cybrneon/head-md-future-of-drawing/process/2023-12-12/readme.md

# Progress of the day

## The Device
This is THE device. With speakers inside, and the micro-switch.
<br>
This is a view without the textile cover on the speaker body.

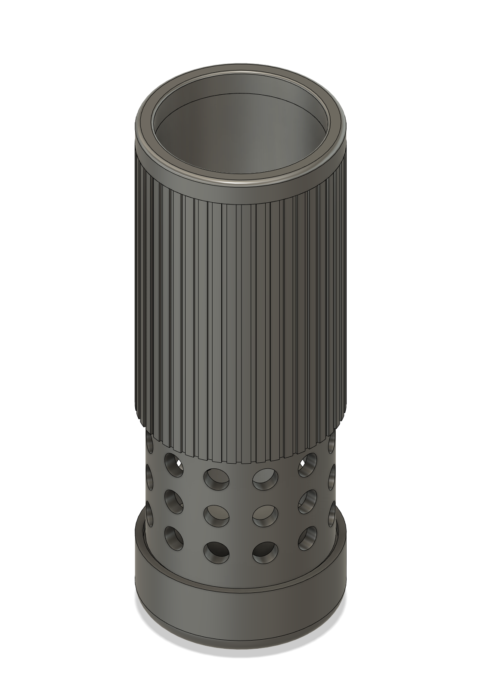
[picture p11: process/2023-12-12/screenshot_shape.png]


## The "Back Box" or "Black box"
This is the box where the RP4 is stored with all the cables, going to the device.

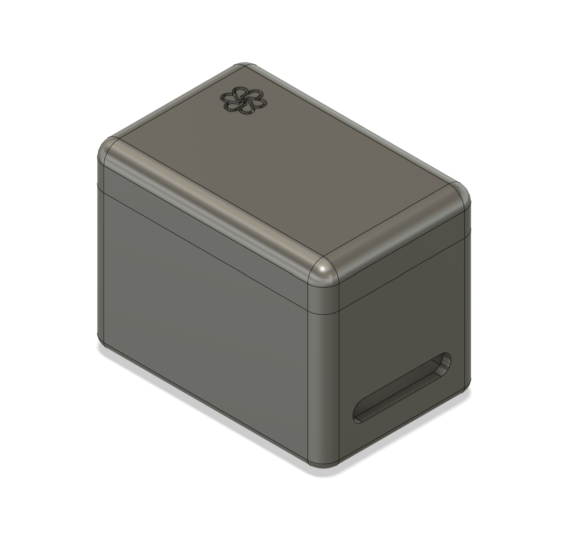
[picture p12: process/2023-12-12/screenshot_shape_blackbox.png]


## Ateliers
Sooooo, yesterday and today was the first day I put my feet in the Prototyping and Metal pool in my whole time at HEAD. So champagne 🍾🥂.
With Fred, I checked how I can make my shape and device come to reality. He told me I can do it with 3d printing. When I checked in the metal pool, Xavier told me that it wasn't possible to do there.

I also checked with the materials, and I think I'll need to find something suitable. For the "aluminium" part of my pen holder, I'll probably spray an aluminium color on it.

Here's a compilation of all the materials I saw there:

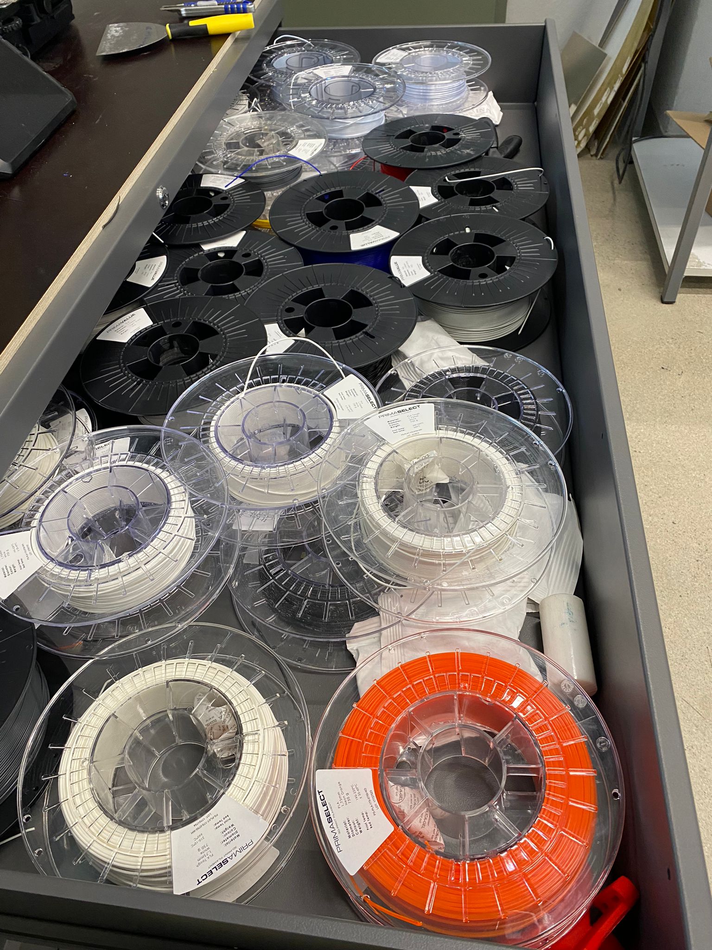
[picture p13: process/2023-12-12/WhatsApp Image 2023-12-12 at 14.30.54.jpeg]

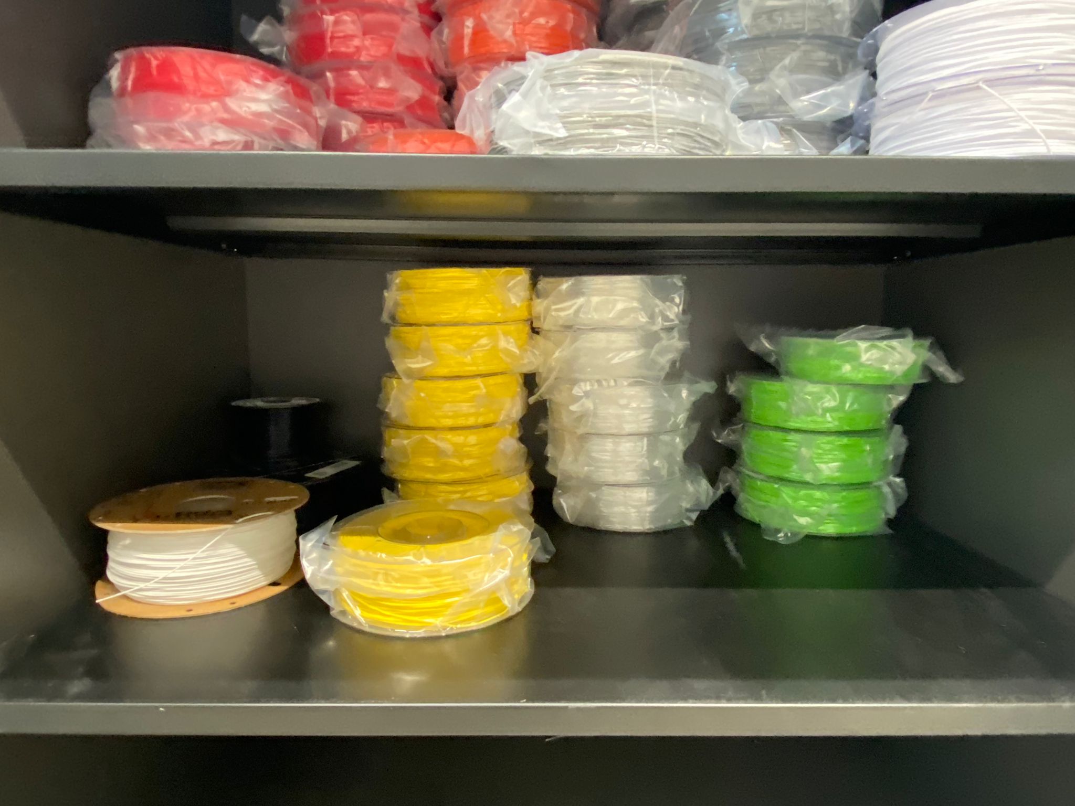
[picture p14: process/2023-12-12/WhatsApp Image 2023-12-12 at 14.30.55.jpeg]

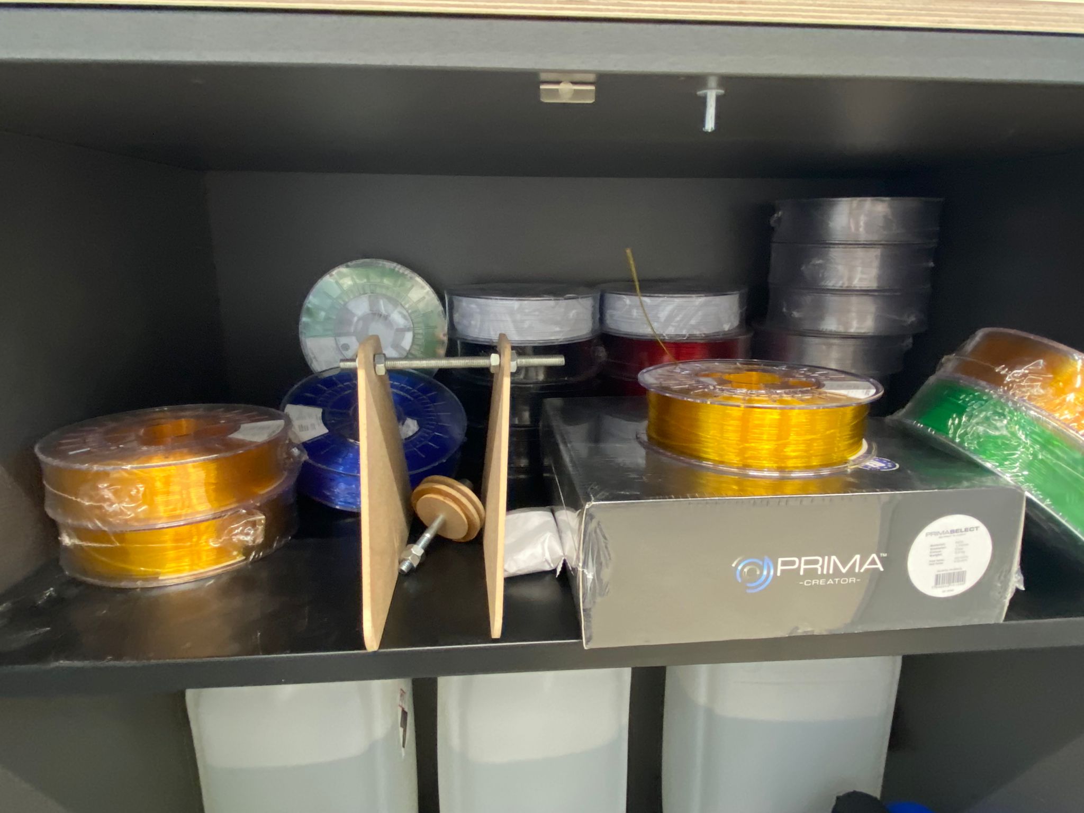
[picture p15: process/2023-12-12/WhatsApp Image 2023-12-12 at 14.30.55_1.jpeg]

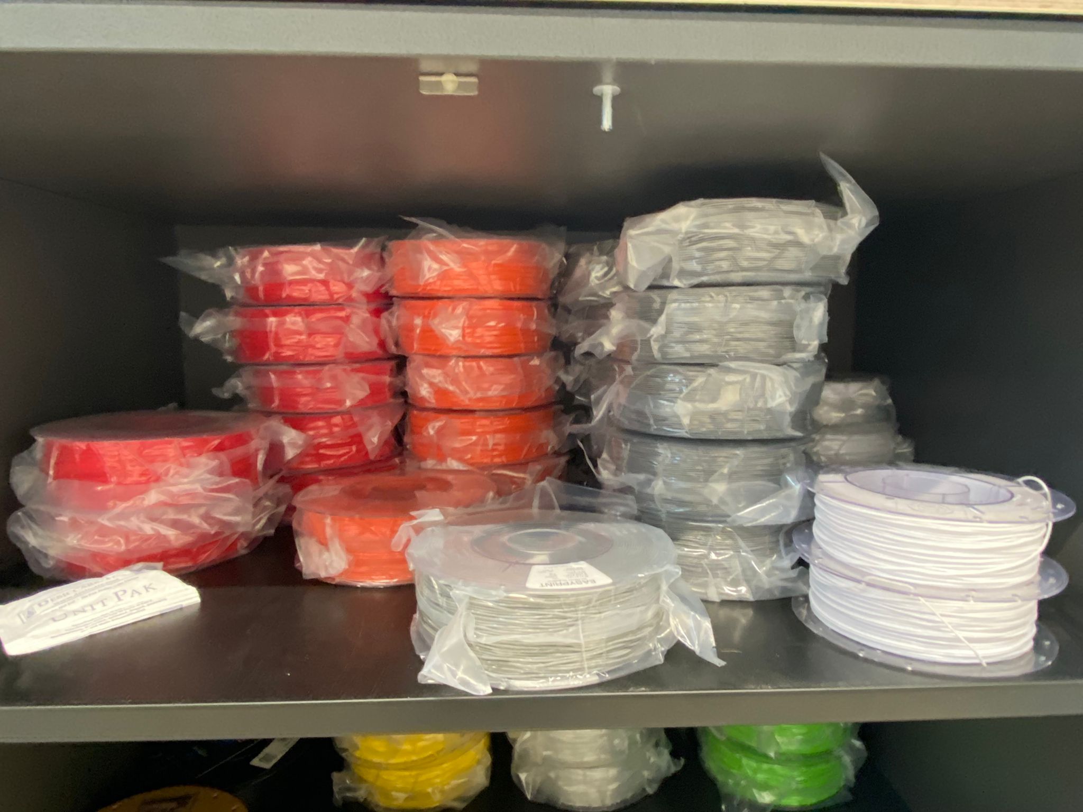
[picture p16: process/2023-12-12/WhatsApp Image 2023-12-12 at 14.30.56.jpeg]

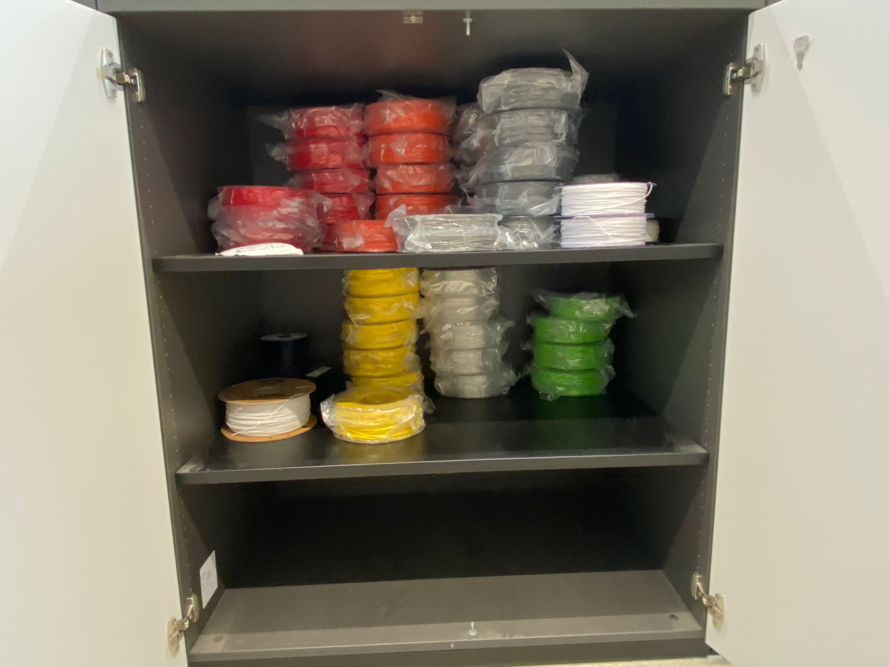
[picture p17: process/2023-12-12/WhatsApp Image 2023-12-12 at 14.30.56_1.jpeg]

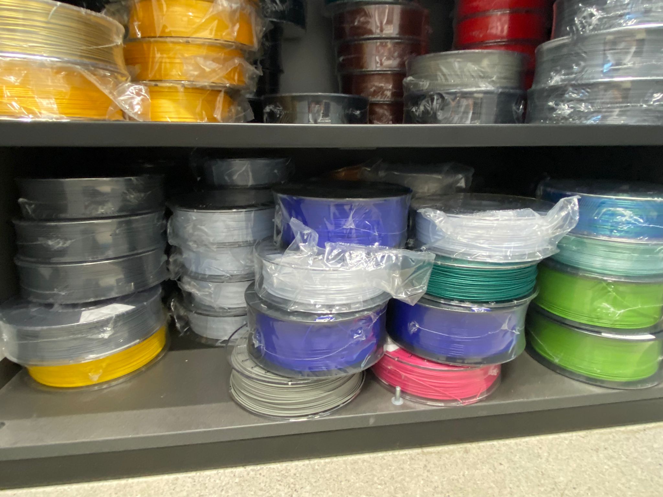
[picture p18: process/2023-12-12/WhatsApp Image 2023-12-12 at 14.30.57.jpeg]

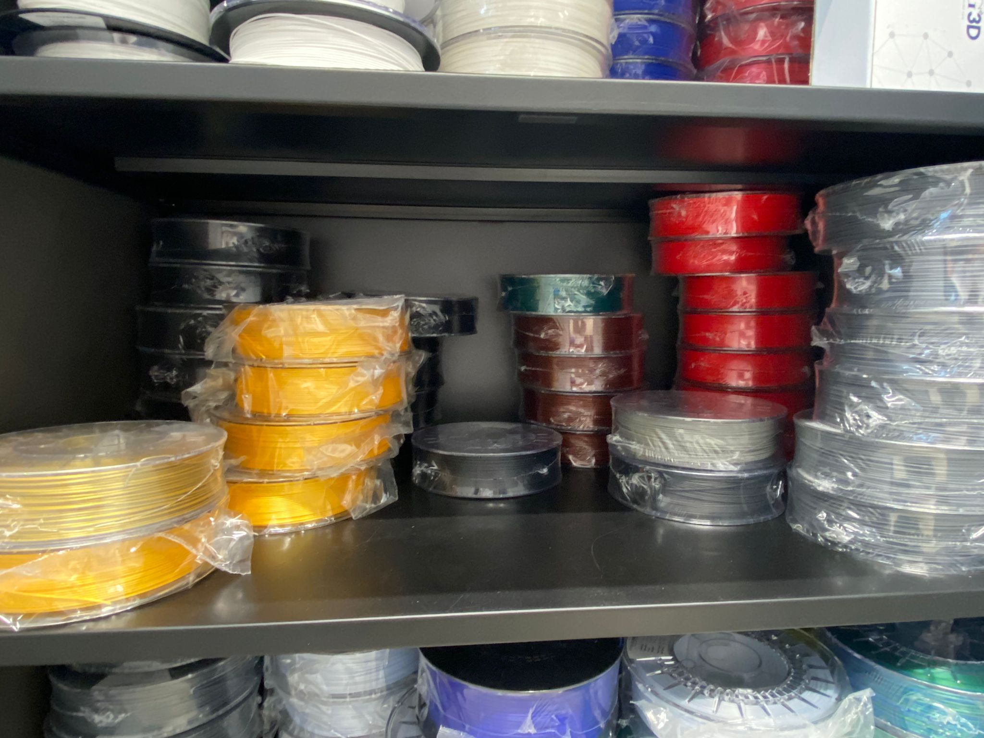
[picture p19: process/2023-12-12/WhatsApp Image 2023-12-12 at 14.30.57_1.jpeg]

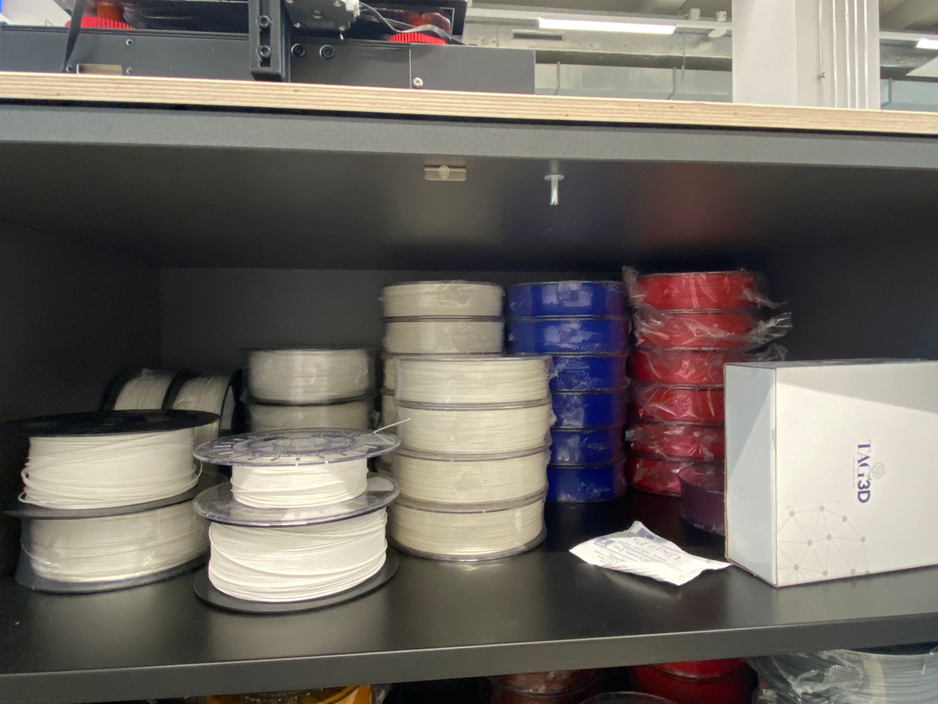
[picture p20: process/2023-12-12/WhatsApp Image 2023-12-12 at 14.30.58.jpeg]

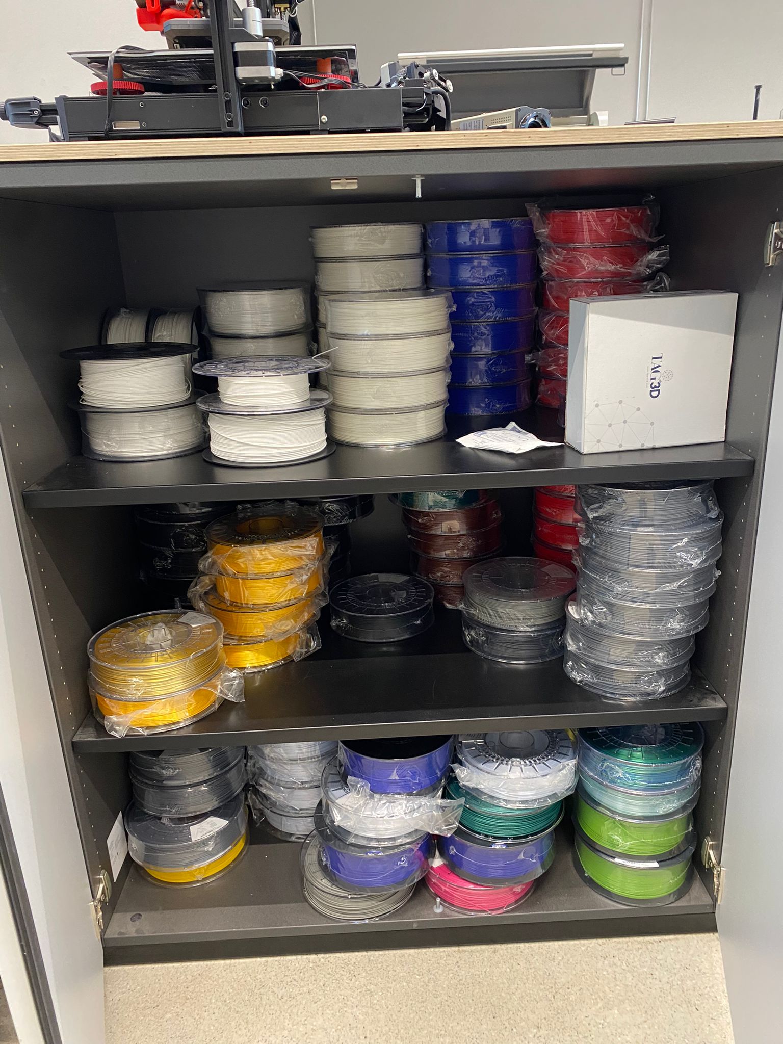
[picture p21: process/2023-12-12/WhatsApp Image 2023-12-12 at 14.30.58_1.jpeg]

<<<<<<< HEAD
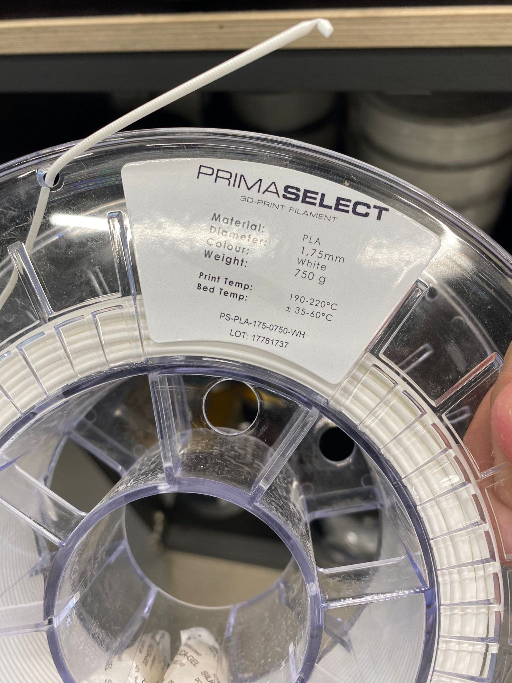
[picture p22: process/2023-12-12/WhatsApp Image 2023-12-12 at 14.30.59.jpeg]

=======


## Preparing for Test Day (D-2)

For the test day, I'm thinking of testing two stories and see what people like more, how they react to them, how inspired they are, etc.

Now I'm asking myself, what can I test on people who never seen or heard of the project?
<br>
-Stories.
<br>
What stories?
<br>
I can probably test the speed of the narration? like if there are blanks in between and if there are not?
<br>
I can also test with a voice synthesis and a recorded one?

### Story 1
Once upon a time, a river.
<br>
Rolling down the Akira Mountains, north of Selestia.
<br>
At the end of the river, a small village, built by a couple after they encountered diamonds in the river.
<br>
And this is why the river is called the Diamond River.
<br>
The couple, named Gigi governed the small village for a few years now, they have their own palace.
<br>
North of the village, a cook and shopkeeper, always ready to delight and make everyday special for the inhabitants of the village, by cooking a delicious stew for instance!
<br>
>>>>>>> parent of 233010a (wednesday morning work)
