cybrneon/head-md-future-of-drawing/process/2023-11-30/readme.md

# It's been a while since the last commit...

We had fun with Arduino, and discovered a lot. It's still a bit too technical, but I hope it will be okay.

## Pictures
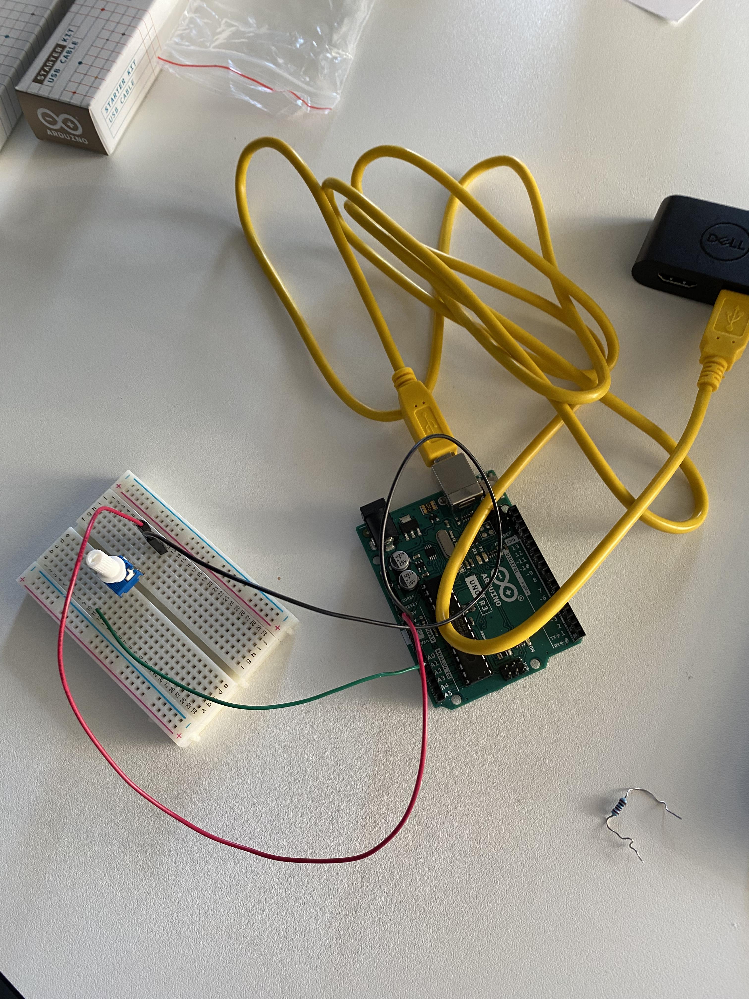
[picture p27: process/2023-11-30/IMG_6413.jpeg]

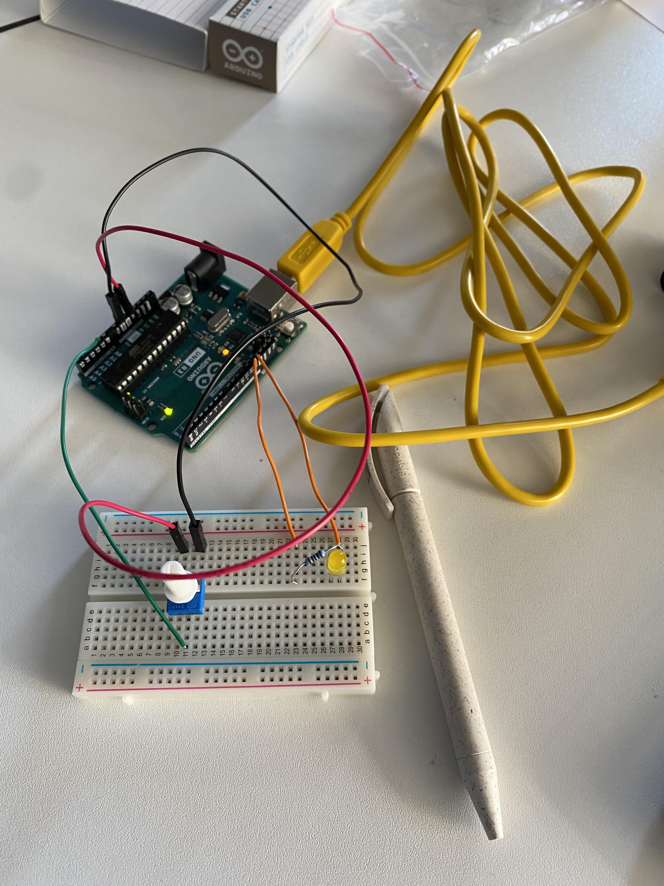
[picture p28: process/2023-11-30/IMG_6414.jpeg]

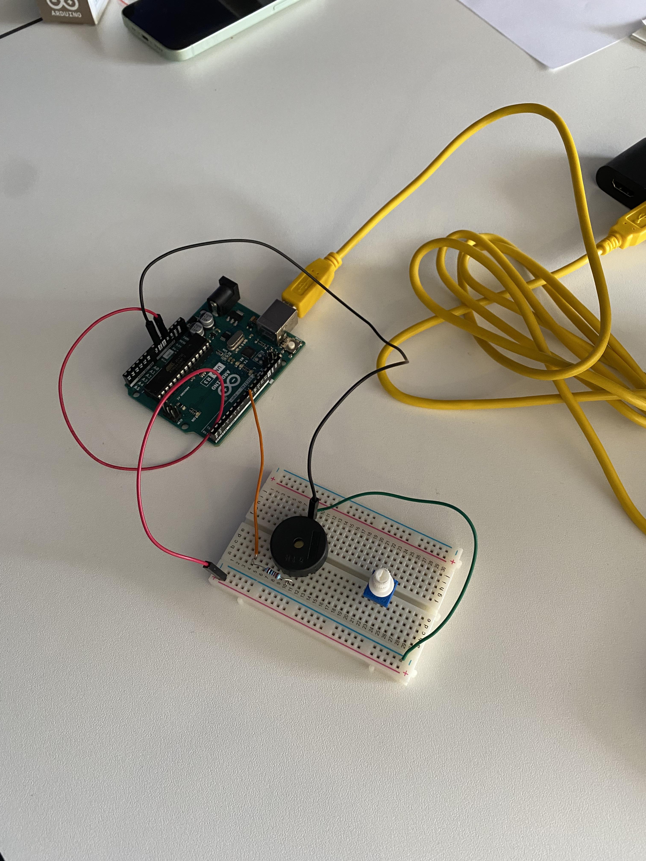
[picture p29: process/2023-11-30/IMG_6421.jpeg]


## Videos
Videos are available on the repo
