cybrneon/head-md-future-of-drawing/process/2023-10-26/readme.md

# Experimentation
We then started to imagine interactions and paper experiments with our subjects. I didn't know how or where to start, so I came back to the cards and drew ones that I then executed into paper prototypes.

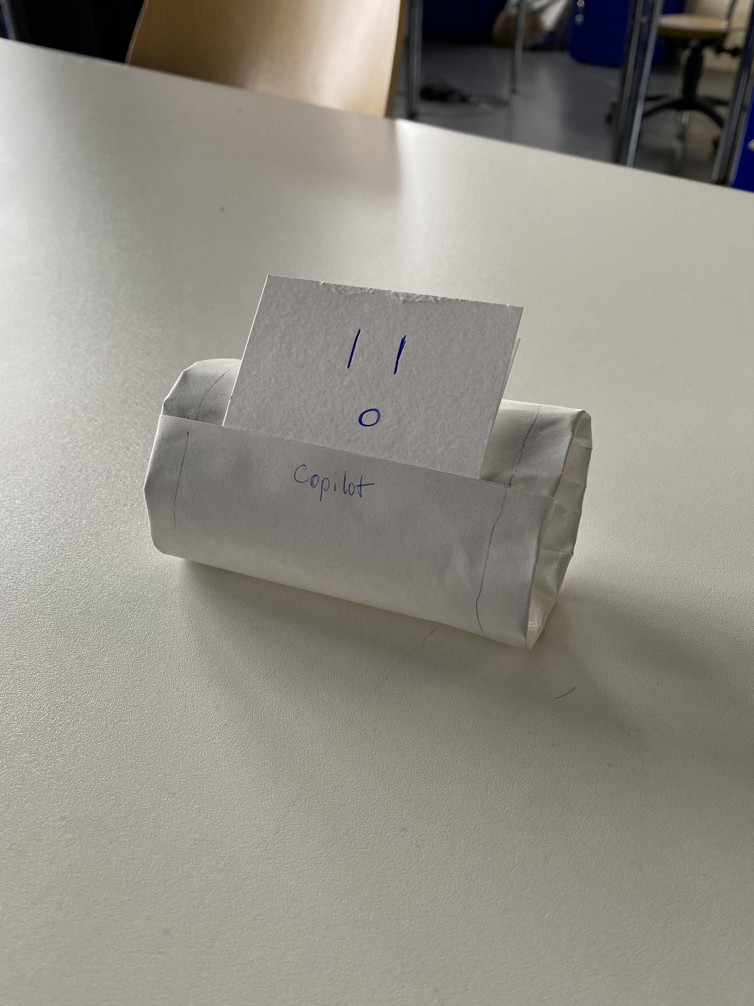
[picture p42: process/2023-10-26/20231026_115851675_iOS.jpeg]
Little Cute Copilot

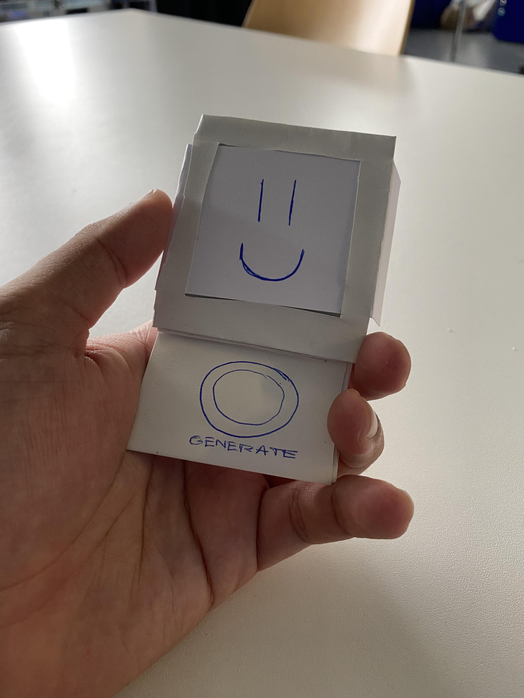
[picture p43: process/2023-10-26/20231026_115932319_iOS.jpeg]
Tamagotchi-like Drawing Experience Generator

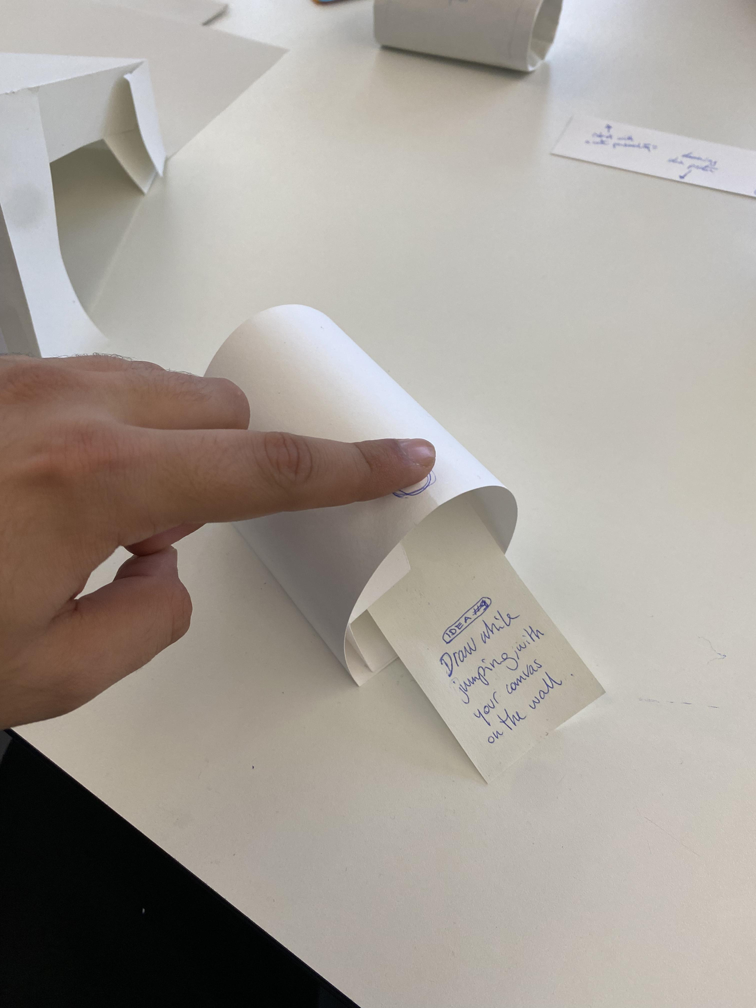
[picture p44: process/2023-10-26/20231030_092805427_iOS.jpeg]
Drawing Experience Generator Printer
