cybrneon/head-md-future-of-drawing/process/2023-12-13/readme.md

# Test Day Prep

## Call with Douglas
We need to have goals. I need to ask questions for me.
> I'm thinking probably testing one story reading it with pauses and seeing how people react and absorb the information to end up drawing. And the same story where I read it in a go without pauses?

This is too subtle!
<br>
I need to see the nature of the story
How much information I give to the user, How much I give to the person that's going to draw.

## Story 1 - original
Once upon a time, a river.
<br>
<br>
Rolling down the Akira Mountains, north of the coutry of Selestia.
<br>
<br>
At the end of the river, a small village, built by a couple after they encountered diamonds in the river.
<br>
<br>
And this is why the river is called the Marvelous Diamond River.
<br>
<br>
The couple, named Gigi governed the small village for a few years now, they even have their own palace.
<br>
<br>
Each year, the tradition states that every first of the month at 3PM, people run from the north to the south of the village, following the river, and dive into the Clear Blue Diamond Lake for a chance to find diamonds.
<br>
<br>
The lakeside is full of people coming from a number of different countries, here to witness the miracle, and why not be part of it.
<br>
<br>
That day in the crowd, a person by the name of Ash just finished their run and dive, was standing next to the lake thinking of what she'll be eating this evening.
<br>
<br>
Ash came to the lakeside with their dog, Ruffus.

## Story 1 - variation 1 (detailed with Bard)

In the heart of the majestic Akira Mountains, nestled amidst the snow-capped peaks and verdant valleys, flowed a magnificent river, its waters shimmering like a cascade of diamonds. This was the marvelous Diamond River, a source of wonder and fascination for the people of Selestia, the land that lay north of its meandering course.
<br>
<br>
Legends whispered of its magical origins, tales of a couple who stumbled upon its crystal-clear depths, discovering amidst the swirling currents a treasure of untold value – diamonds, embedded within the riverbed like glittering stars. Enthralled by their discovery, the couple established a small village at the river's end, naming it Diamond Village in honor of its precious namesake.
<br>
<br>
Over the centuries, the village grew in prosperity, its inhabitants living in harmony with the river's bounty. The villagers, guided by the wisdom of their ancestors, established a tradition that echoed the river's magical essence. Every first of the month, at the precise hour of three in the afternoon, they would embark on a grand procession, traversing the length of the village, following the river's winding path.
<br>
<br>
Upon reaching the Clear Blue Diamond Lake, a mesmerizing body of water that mirrored the heavens, the villagers would plunge into its depths, their hearts filled with anticipation. The lake, as if responding to their collective desire, would reveal its hidden treasures, scattering diamonds across the surface like a shower of celestial sparks.
<br>
<br>
This extraordinary spectacle drew visitors from far and wide, each hoping to witness the magical transformation and perhaps claim a diamond of their own. From the bustling streets of distant cities to the tranquil shores of neighboring kingdoms, people journeyed to Diamond Village, their eyes sparkling with excitement and a touch of disbelief.
<br>
<br>
On this particular first of the month, a young woman named Ash joined the throng of eager participants. Ash, accompanied by her loyal canine companion, Ruffus, had traveled from a distant land, her heart filled with a mix of curiosity and determination. She had heard tales of the Marvelous Diamond River and the village that lay at its end, tales of wonder and enchantment that had captured her imagination.
<br>
<br>
As the procession reached the Clear Blue Diamond Lake, Ash and Ruffus joined the mass of divers, their bodies plunging into the cool, refreshing waters. Around them, the air was filled with a collective gasp as the surface of the lake ignited with a dazzling display of diamonds, their brilliance reflecting the sun's radiant rays.
<br>
<br>
With hearts pounding and eyes wide with excitement, Ash and Ruffus emerged from the lake, their hands clutching their newfound treasures. Ash's heart swelled with joy as she held the sparkling diamond, its facets twinkling like a constellation of stars. She had not only witnessed the magic of the Marvelous Diamond River but had also become part of its enduring legend.
<br>
<br>
As the villagers celebrated their victory, Ash and Ruffus sat by the lakeside, savoring their newfound wealth and the memories of their extraordinary adventure. The sun began to set, casting a warm glow over the village and the majestic Akira Mountains, a perfect ending to a day filled with wonder and enchantment.

### -> Asking Bard to keep going with this story beggining
Ash and Ruffus were walking along the river bank, enjoying the cool breeze and the beautiful scenery of the Akira Mountains. The water in the river was crystal clear and sparkled in the sunlight, reflecting the lush green trees that lined the banks. Ash was lost in thought, thinking about the upcoming diamond dive. She had heard stories about people finding huge diamonds in the Clear Blue Diamond Lake, and she couldn't help but feel a little excited about the possibility of being one of them.
<br>
<br>
As they approached the lake, Ash could see the crowds of people already gathered on the shore. Everyone was eager to get into the water and start searching for diamonds. Ash and Ruffus joined the line and waited their turn.
<br>
<br>
Finally, it was Ash's turn to dive into the lake. She took a deep breath and plunged into the water. The water was cold and refreshing, and she could see the sunlight filtering down from the surface. She swam down to the bottom of the lake and started searching for diamonds.
<br>
<br>
After a few minutes, Ash spotted something shiny on the bottom of the lake. She swam over to it and picked it up. It was a small diamond, but it was still beautiful. Ash was thrilled! She swam back to the surface and showed the diamond to Ruffus, who wagged his tail excitedly.
<br>
<br>
Ash and Ruffus joined the other people who had found diamonds and celebrated their good fortune. They all agreed that it was a great day to be in Selestia.
<br>
<br>
Later that evening, Ash and Ruffus were enjoying a delicious dinner of grilled fish and vegetables. They were feeling very happy and content. Ash had had a wonderful day, and she was grateful for the opportunity to experience the miracle of the Marvelous Diamond River.

### -> Asking ChatGPT to keep going with this story beggining
As Ash caught her breath, she marveled at the sparkling water of the Clear Blue Diamond Lake. The sun dipped low on the horizon, casting a warm golden glow over the village and turning the water into a mesmerizing sea of reflections. Ruffus, her loyal dog, wagged his tail enthusiastically, seemingly as captivated by the spectacle as the humans around them.
<br>
<br>
The tradition of diving for diamonds had been a part of Ash's life for as long as she could remember. Her parents, avid treasure hunters, had regaled her with tales of their own diamond discoveries in the Marvelous Diamond River. Now, as an adult, Ash continued the family tradition, seeking not just wealth but also the thrill of the chase.
<br>
<br>
While many participants eagerly scanned the lake bed for the elusive gems, Ash's mind was preoccupied with a different kind of treasure – a cozy meal waiting for her at home. She had recently discovered a quaint little bakery in the village that boasted the most delectable pastries. As the sun dipped lower, Ash decided to wrap up her diamond quest and head to the bakery before it closed.
<br>
<br>
With Ruffus trotting faithfully by her side, Ash strolled through the lively village square. The air was filled with the sweet aroma of freshly baked goods, and the sound of laughter and chatter enveloped the surroundings. The villagers prepared for the evening festivities, which included a grand feast in celebration of the monthly ritual.
<br>
<br>
As Ash reached the bakery, she was greeted by the warm smile of the baker, an elderly woman named Elara, known for her culinary prowess. The tantalizing display of pastries and cakes beckoned Ash, and she couldn't resist ordering an assortment to enjoy later in the evening.
<br>
<br>
With a bag full of pastries in hand, Ash made her way back to the lakeside. The sun had dipped below the horizon, and the village was bathed in the soft glow of lanterns and the radiant moonlight. The excitement in the air was palpable as villagers prepared for the feast, sharing stories of their diamond dives and exchanging laughter.
<br>
<br>
Ash found a quiet spot by the lake, where the gentle lapping of the water provided a soothing backdrop. Ruffus settled down beside her, his eyes gleaming with contentment. As the villagers reveled in the festivities, Ash indulged in the delightful pastries, savoring each bite.
<br>
<br>
Little did she know that this seemingly ordinary evening held the promise of unexpected adventures and discoveries. The Marvelous Diamond River, with its mystical allure, was about to weave another chapter into the tapestry of Ash's life, one filled with intrigue and the magic of the Akira Mountains.

# Other Stuff
I've been thinking of a name for my project because I kept the project name "Morpheus Project". It's a project name, but I want a really cool name for my device and assistant. Why not keep Morpheus? or find another name?

I also tested 3d printing!
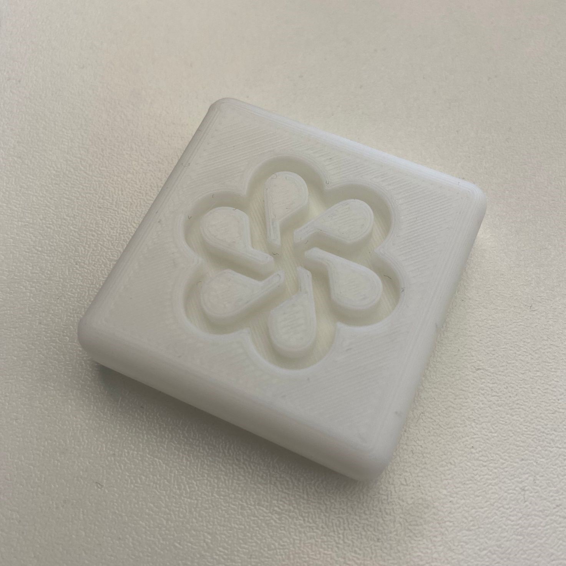
[picture p53: process/2023-12-13/3d_print_test.jpeg]
