cybrneon/head-md-future-of-drawing/process/2023-10-25/readme.md

# Prototyping? with Paper!
## First Try
At first, I drew the following cards:
- Inks
- Poker Face
- Figuration
- Peltier

I then made an interactive Captcha machine that asks you to draw something on it to confirm you're human, with a voice that asks you why you're drawing things the way you're drawing them and not giving any emotion.

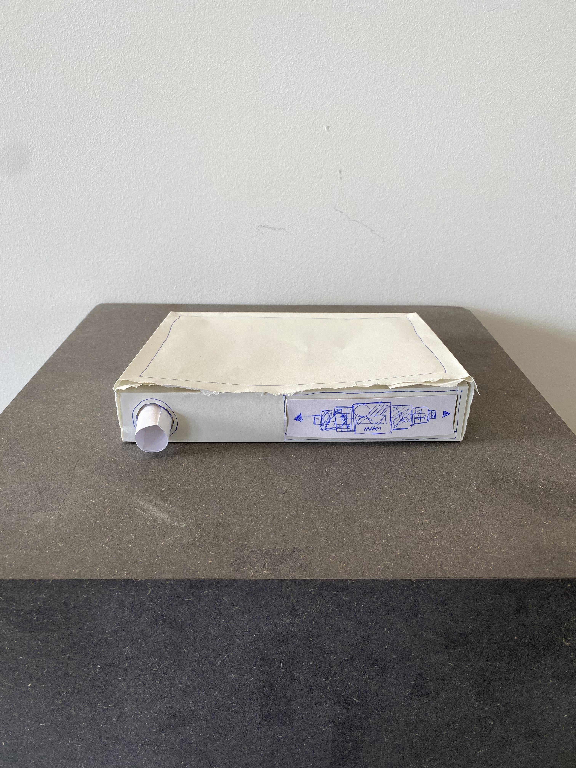
[picture p57: process/2023-10-25/20231025_130053381_iOS.jpeg]

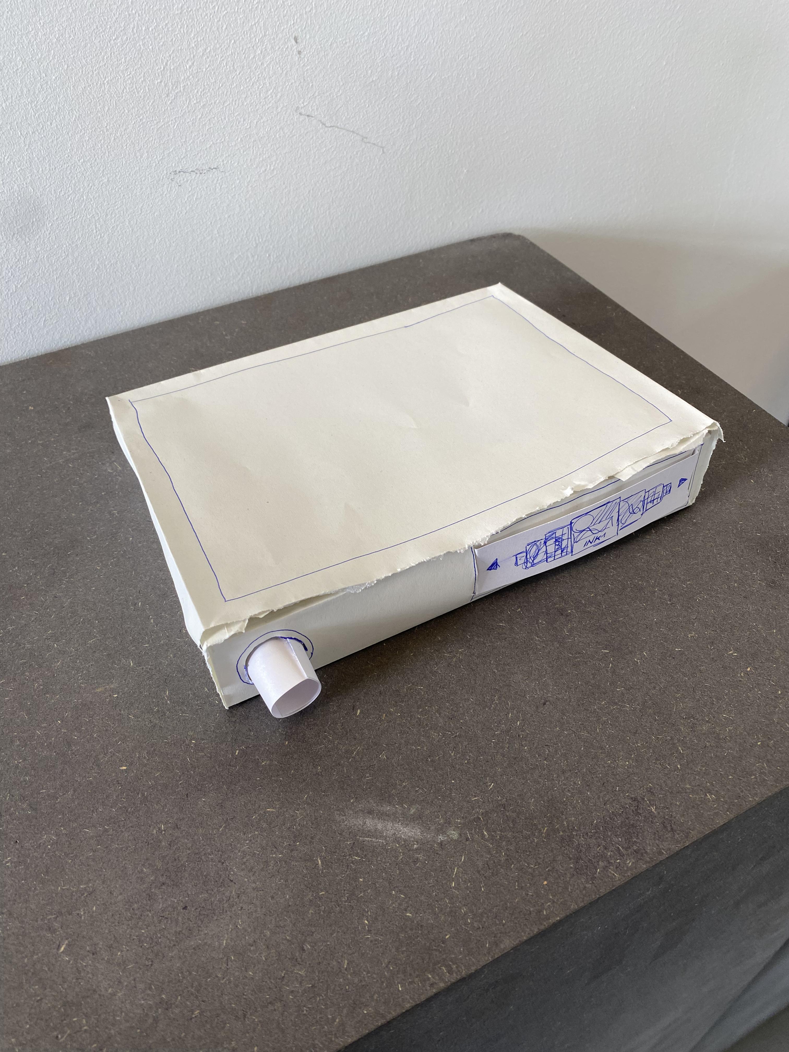
[picture p58: process/2023-10-25/20231025_130104790_iOS.jpeg]

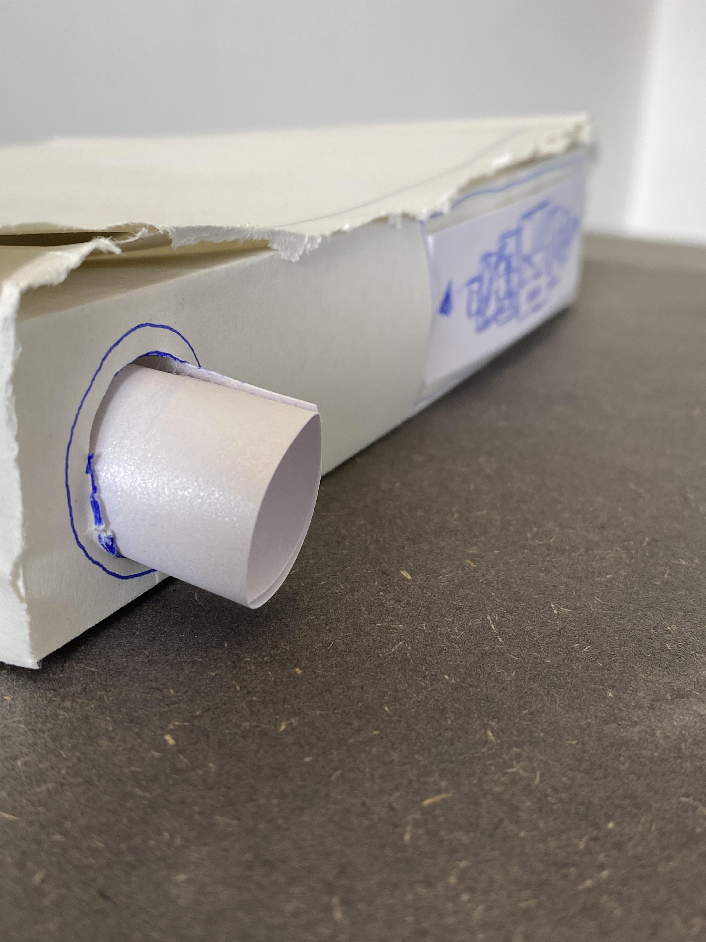
[picture p59: process/2023-10-25/20231025_130112993_iOS.jpeg]

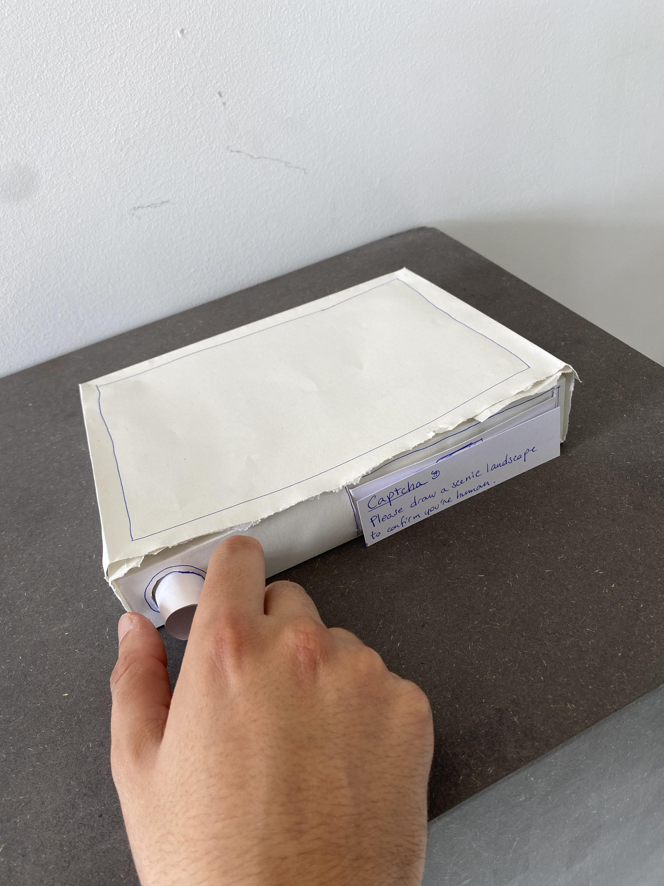
[picture p60: process/2023-10-25/20231025_130137430_iOS.jpeg]
