cybrneon/head-md-future-of-drawing/form/img/snapshot_shape2.png

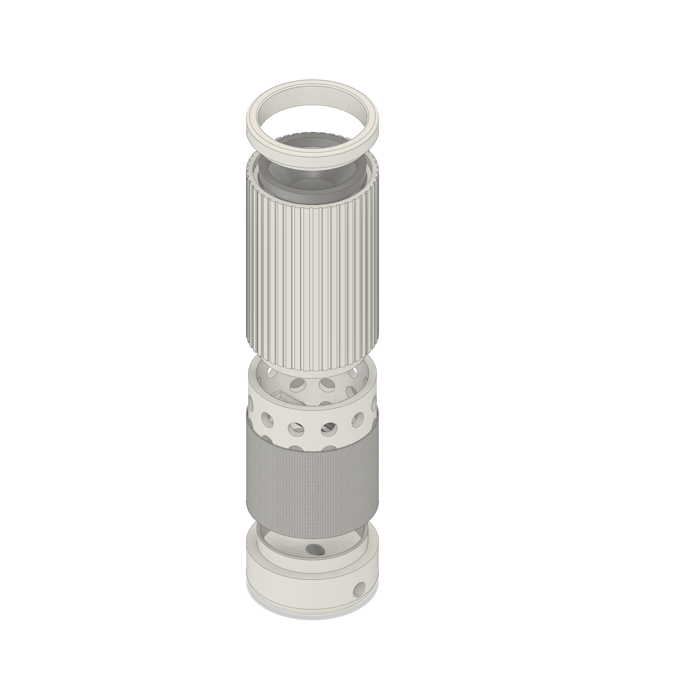
form/img/snapshot_shape2.png
