cybrneon/head-md-future-of-drawing/form/render/CdA_FinalSketch_render3.png

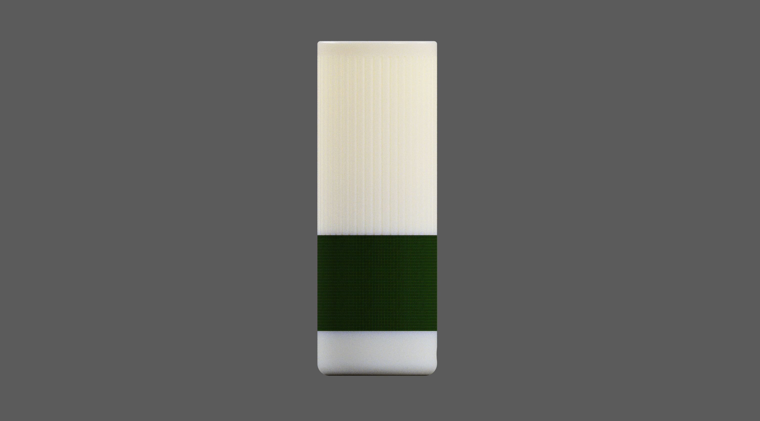
form/render/CdA_FinalSketch_render3.png
