cybrneon/head-md-future-of-drawing/presentations/branding/morpheus-beta-colorpalette.png

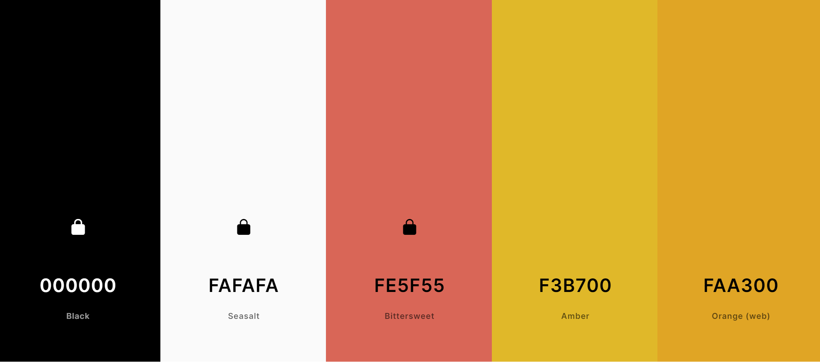
presentations/branding/morpheus-beta-colorpalette.png
