cybrneon/head-md-future-of-drawing/presentations/concept-presentation-2023-11-16/Dossier_CdA_Concept_InDesign/Links/IMG_6370.jpg

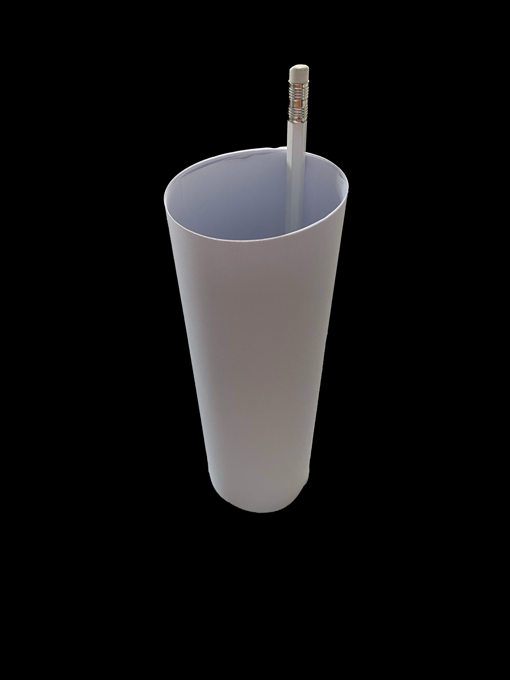
presentations/concept-presentation-2023-11-16/Dossier_CdA_Concept_InDesign/Links/IMG_6370.jpg
