cybrneon/head-md-future-of-drawing/presentations/concept-presentation-2023-11-16/Dossier_CdA_Concept_InDesign/Links/radio_1.jpg

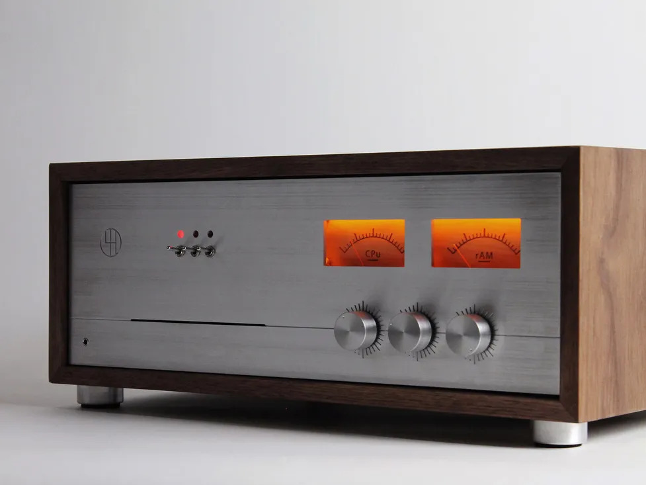
presentations/concept-presentation-2023-11-16/Dossier_CdA_Concept_InDesign/Links/radio_1.jpg
