cybrneon/head-md-future-of-drawing/presentations/final-presentation-folder-2024-01-17/Links/morpheus-userjourney.png

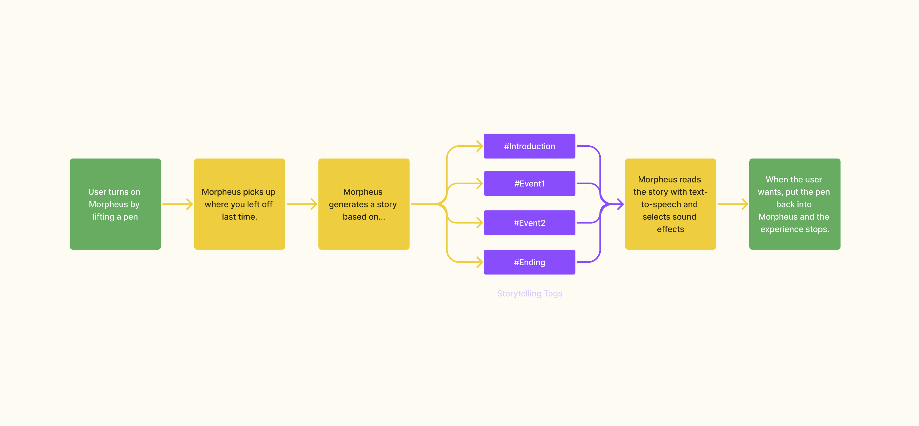
presentations/final-presentation-folder-2024-01-17/Links/morpheus-userjourney.png
