cybrneon/head-md-future-of-drawing/process/2023-10-19_20/20231019_132728396_iOS.jpeg

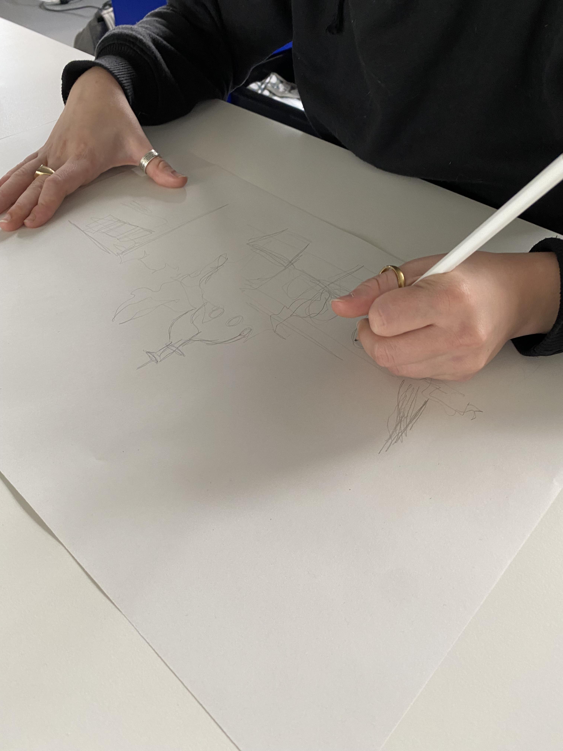
process/2023-10-19_20/20231019_132728396_iOS.jpeg
