cybrneon/head-md-future-of-drawing/process/2023-10-19_20/20231020_075834999_iOS.jpeg

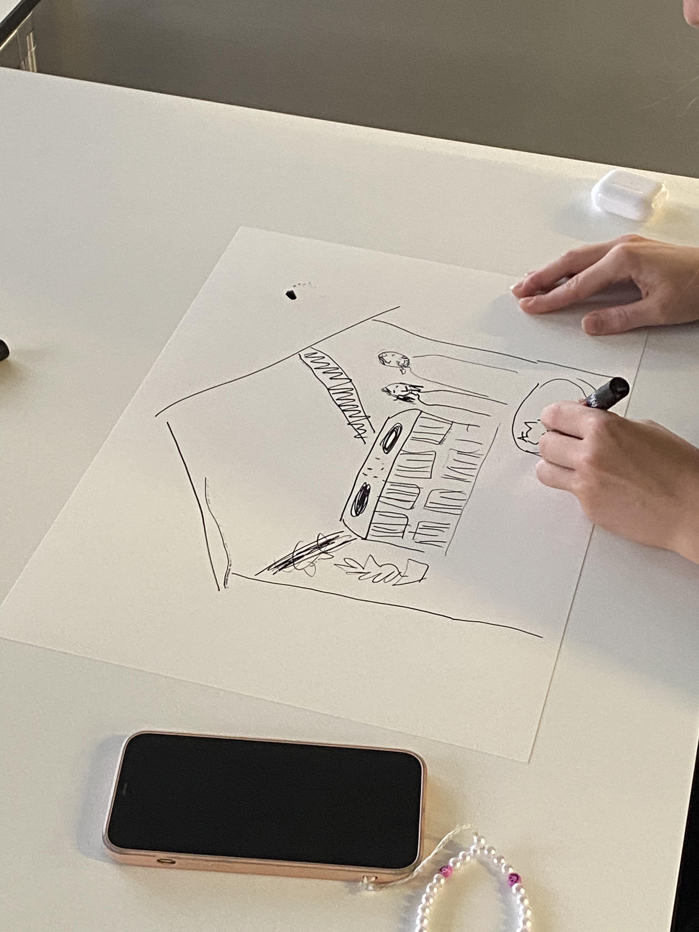
process/2023-10-19_20/20231020_075834999_iOS.jpeg
