cybrneon/head-md-future-of-drawing/process/2023-10-19_20/20231020_080150618_iOS.jpeg

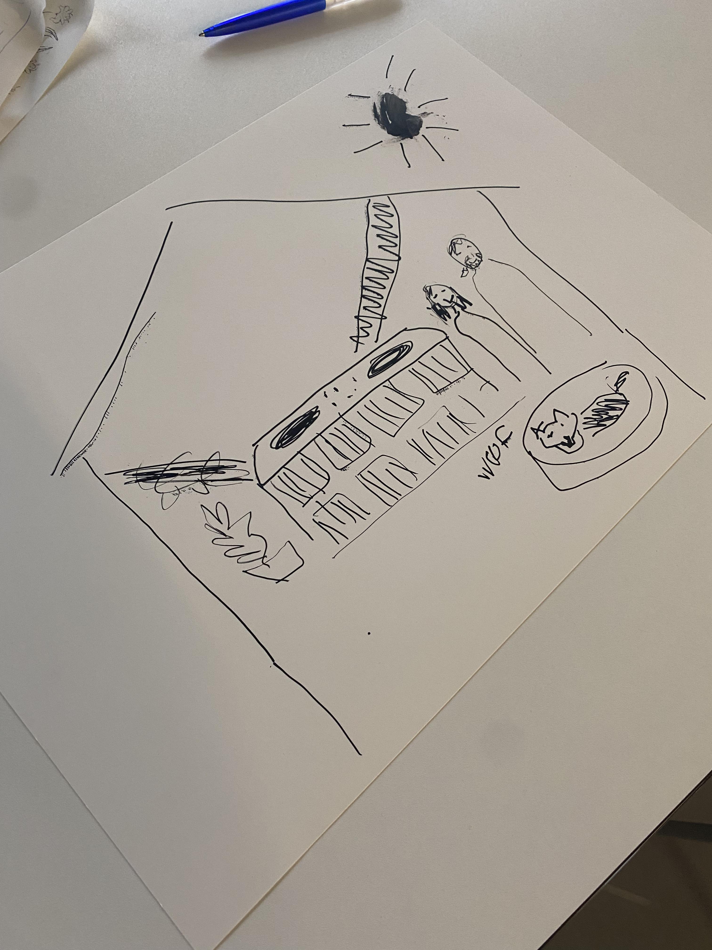
process/2023-10-19_20/20231020_080150618_iOS.jpeg
