cybrneon/head-md-future-of-drawing/process/2023-10-25/20231025_130244025_iOS.jpeg

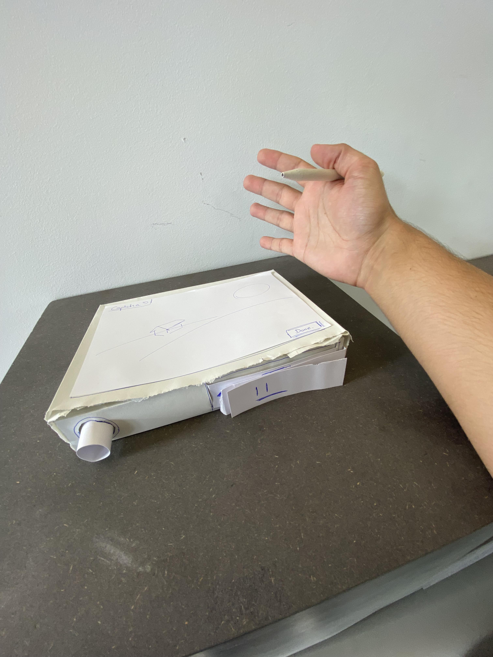
process/2023-10-25/20231025_130244025_iOS.jpeg
