cybrneon/head-md-future-of-drawing/process/2023-10-26/20231026_120012041_iOS.jpeg

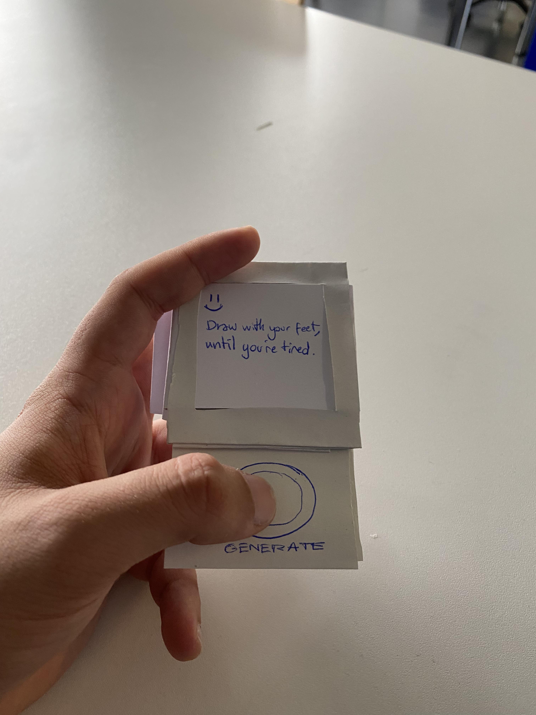
process/2023-10-26/20231026_120012041_iOS.jpeg
