cybrneon/head-md-future-of-drawing/process/2023-10-26/20231030_092759936_iOS.jpeg

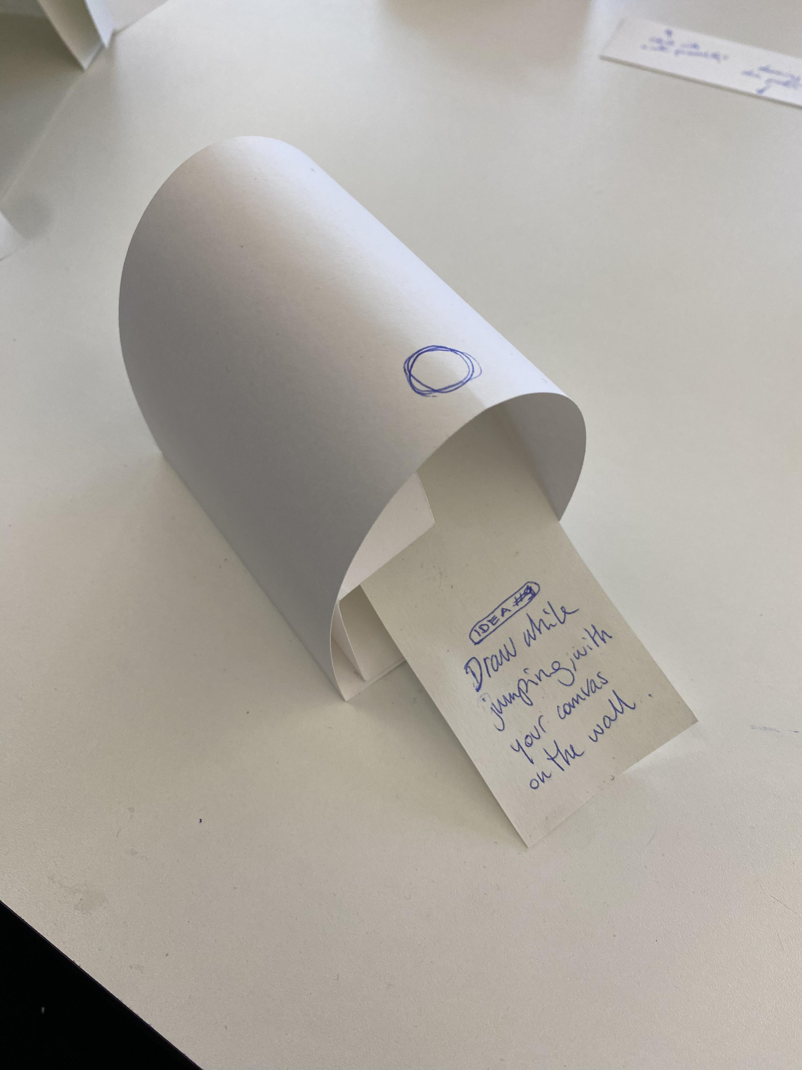
process/2023-10-26/20231030_092759936_iOS.jpeg
