cybrneon/head-md-future-of-drawing/process/2023-10-30/20231030_092852672_iOS.jpeg

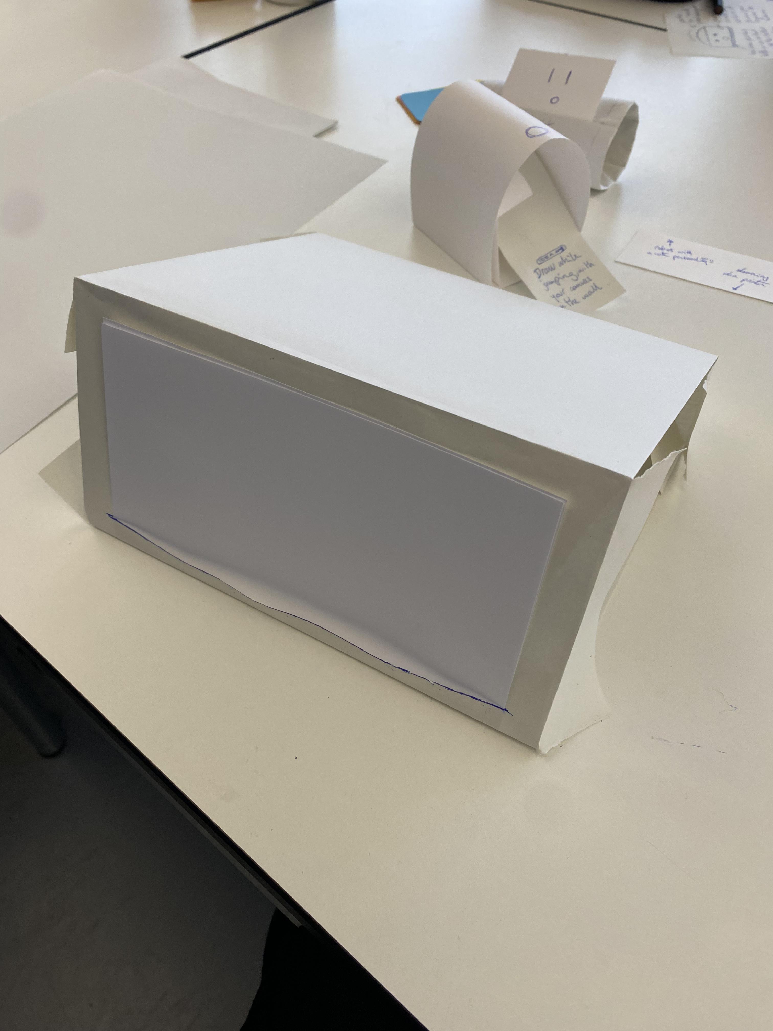
process/2023-10-30/20231030_092852672_iOS.jpeg
