cybrneon/head-md-future-of-drawing/process/2023-10-30/20231030_143424386_iOS.jpeg

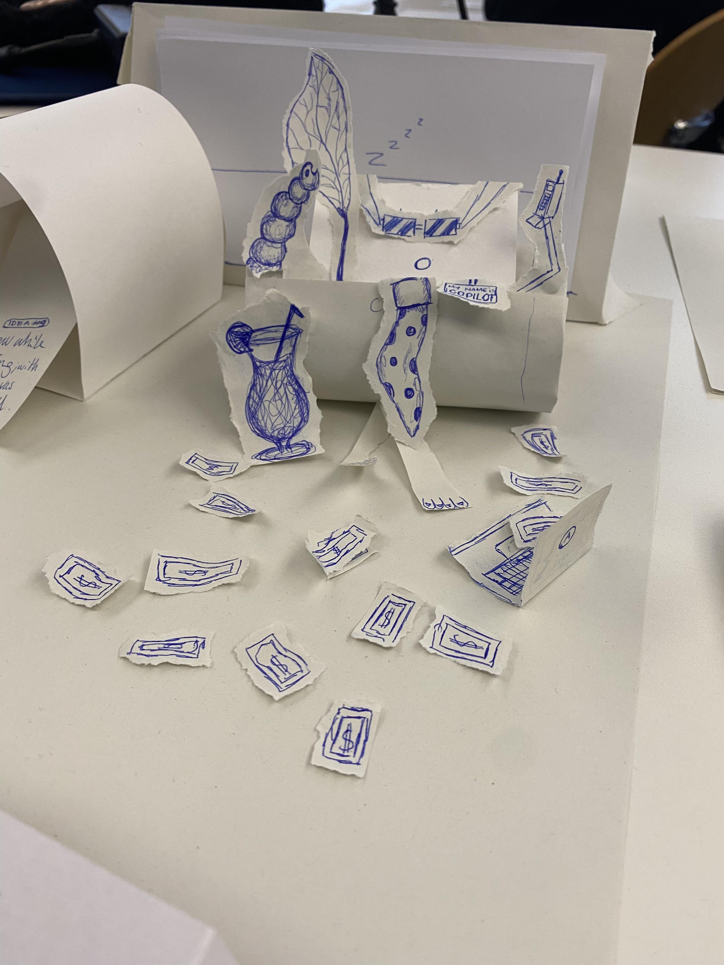
process/2023-10-30/20231030_143424386_iOS.jpeg
