cybrneon/head-md-future-of-drawing/process/2023-11-01/20231101_100316862_iOS.jpeg

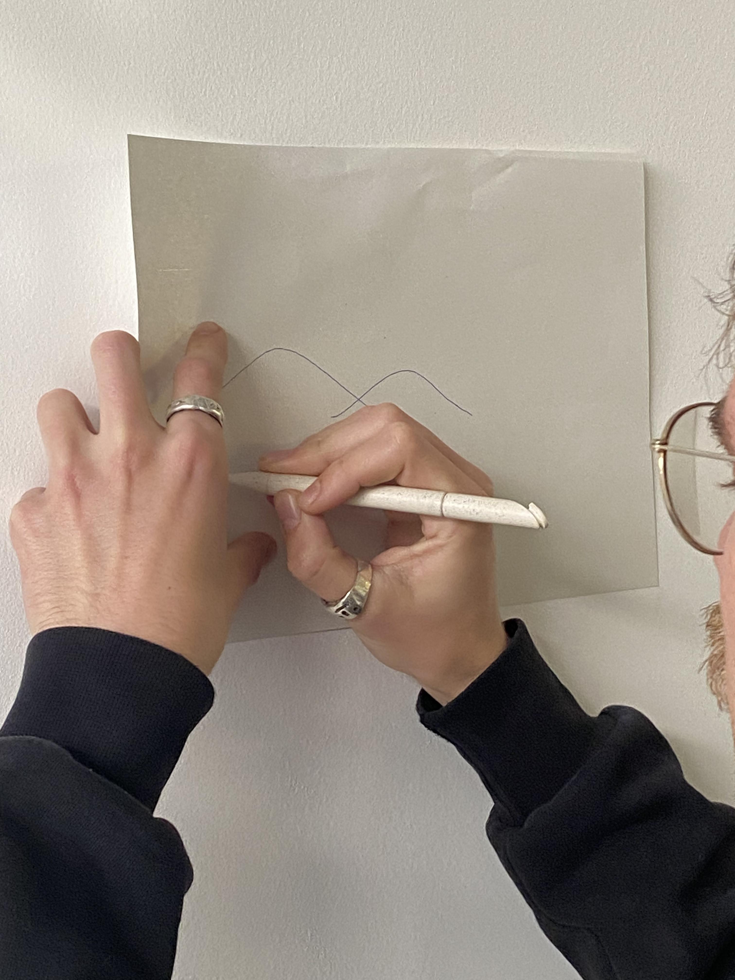
process/2023-11-01/20231101_100316862_iOS.jpeg
