cybrneon/head-md-future-of-drawing/process/2023-11-01/20231101_101724469_iOS.jpeg

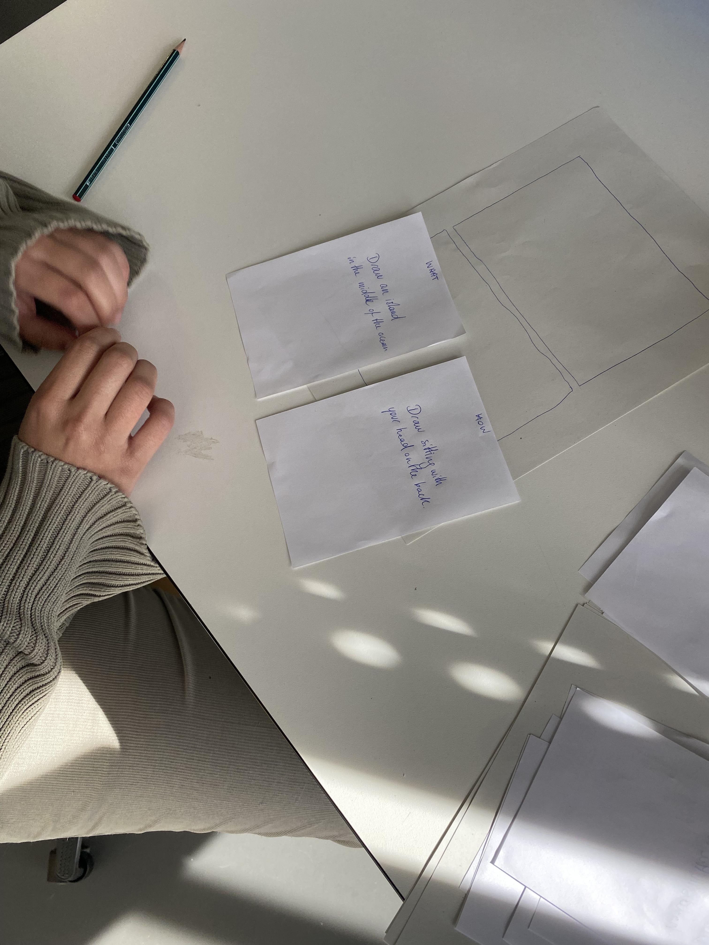
process/2023-11-01/20231101_101724469_iOS.jpeg
