cybrneon/head-md-future-of-drawing/process/2023-11-01/20231101_104921781_iOS.jpeg

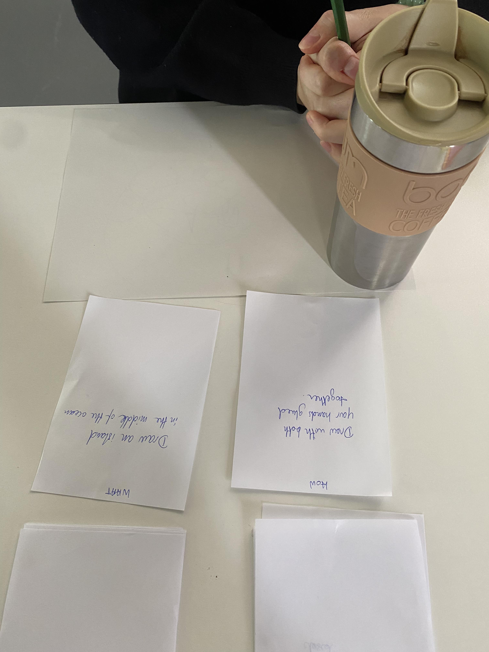
process/2023-11-01/20231101_104921781_iOS.jpeg
