cybrneon/head-md-future-of-drawing/process/2023-11-01/20231101_105053932_iOS.jpeg

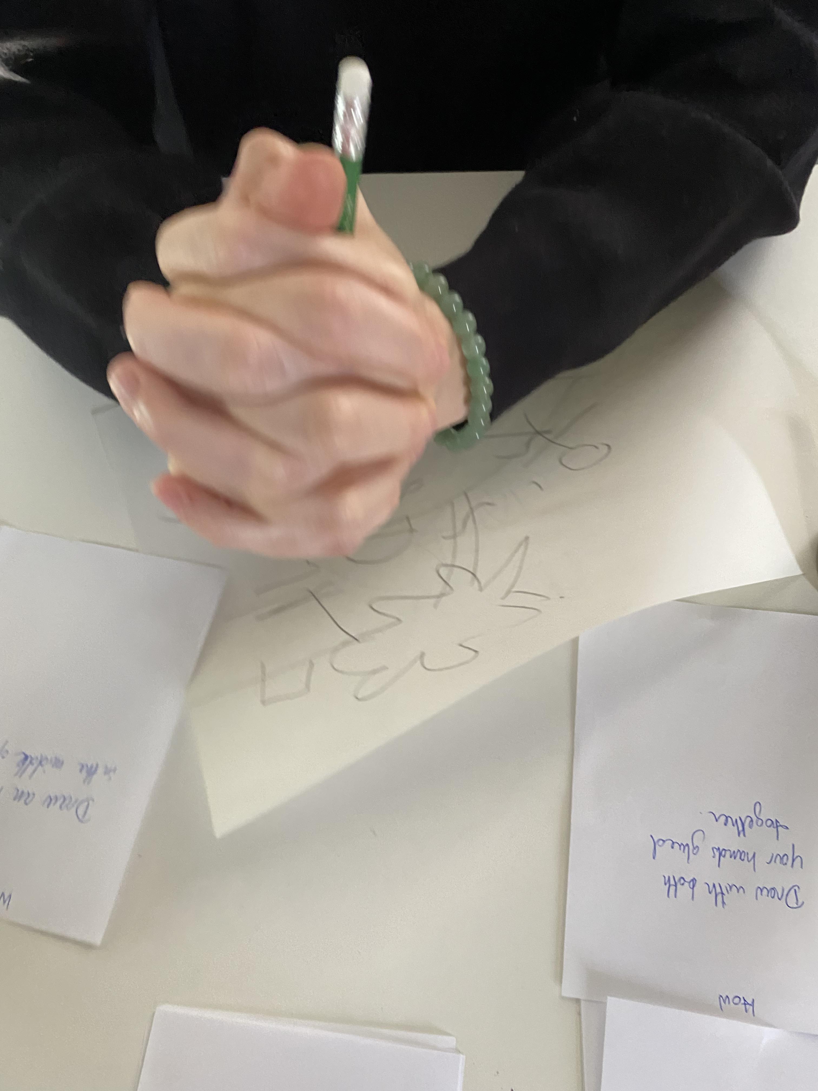
process/2023-11-01/20231101_105053932_iOS.jpeg
