cybrneon/head-md-future-of-drawing/process/2023-11-13/IMG_subject1_01.jpeg

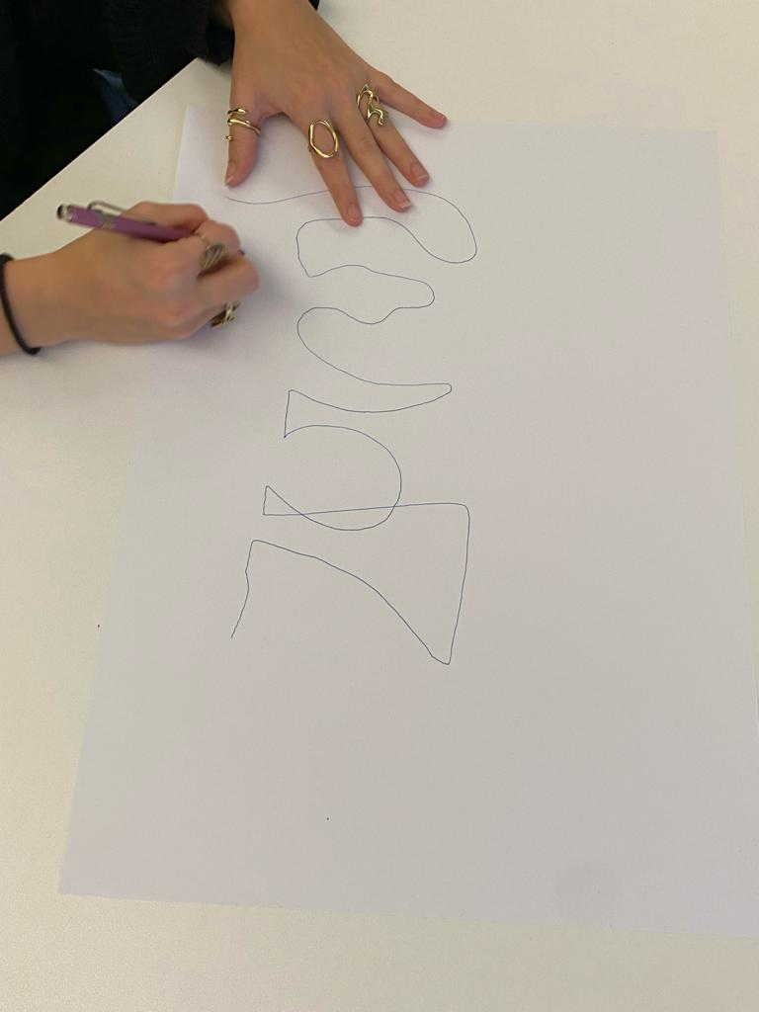
process/2023-11-13/IMG_subject1_01.jpeg
