cybrneon/head-md-future-of-drawing/process/2023-11-13/IMG_subject1_03.jpeg

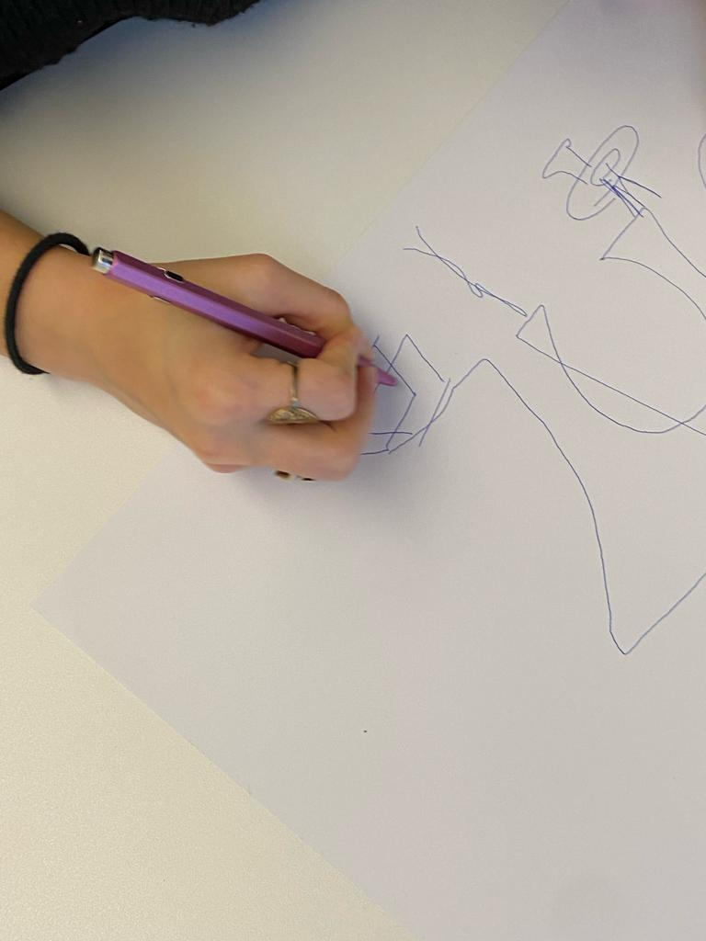
process/2023-11-13/IMG_subject1_03.jpeg
