cybrneon/head-md-future-of-drawing/process/2023-11-14/IMG_6363.jpeg

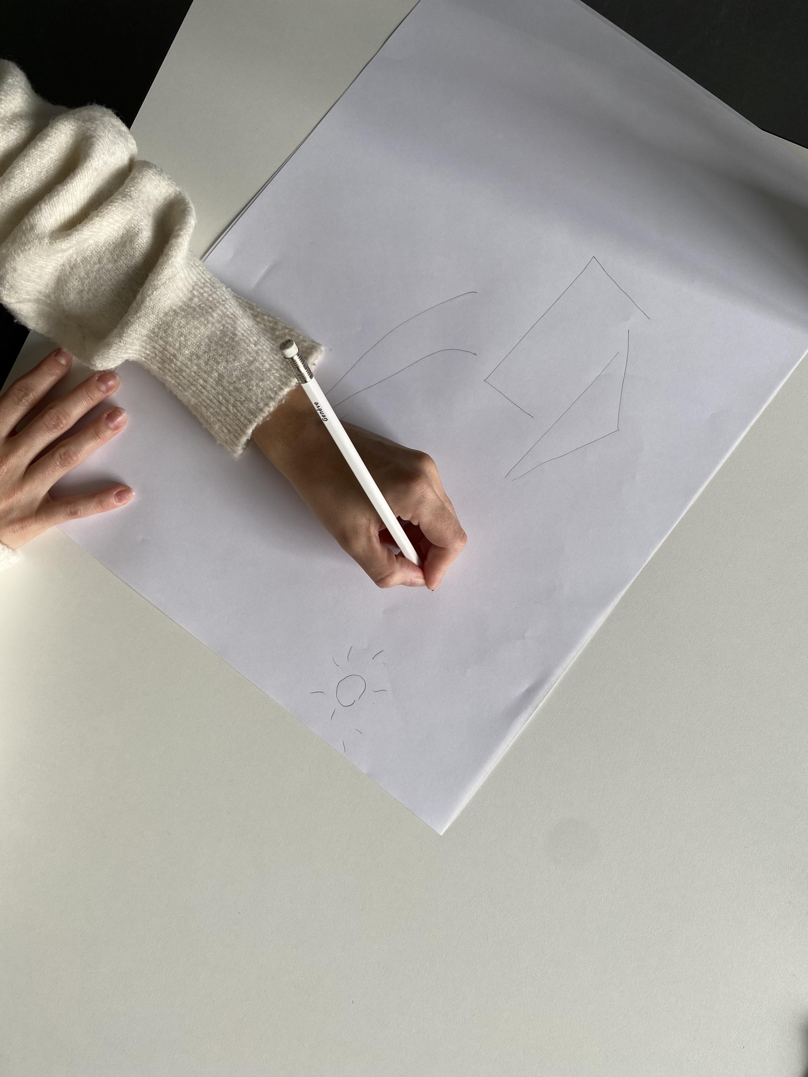
process/2023-11-14/IMG_6363.jpeg
