cybrneon/head-md-future-of-drawing/process/2023-11-15/DrawTheMapOfACity_diagram.png

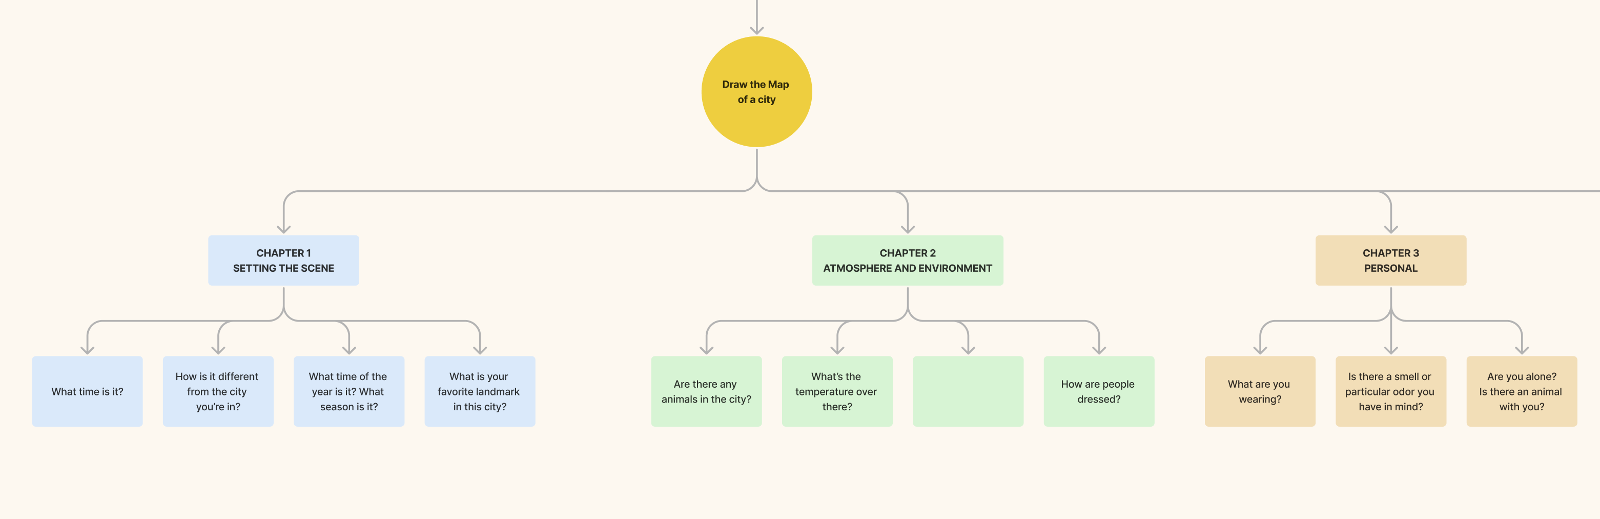
process/2023-11-15/DrawTheMapOfACity_diagram.png
