cybrneon/head-md-future-of-drawing/electronics/tutorials_with_pierre/Trying_Arduino_5_OtherInputs/Trying_Arduino_5_OtherInputs.ino

#define LED 13

int lum = 15; //brightness between 0 and 20

void setup() {
  Serial.begin(9600);
  pinMode(LED, OUTPUT);
}

void loop() {
  // Will get a value between 0 and 1023
  int value = analogRead(A1);
  Serial.println(value);

  // Map the value from 0-1023 range to 0-20 range
  lum = map (value, 0, 1023, 0, 20);

  digitalWrite(LED, HIGH);
  delay(lum);
  digitalWrite(LED, LOW);
  delay(20-lum);
}
